bschulz1701/Project-Hedorah/Mechanical/Mrk 3 Body Assembly/VertMount.SLDASM

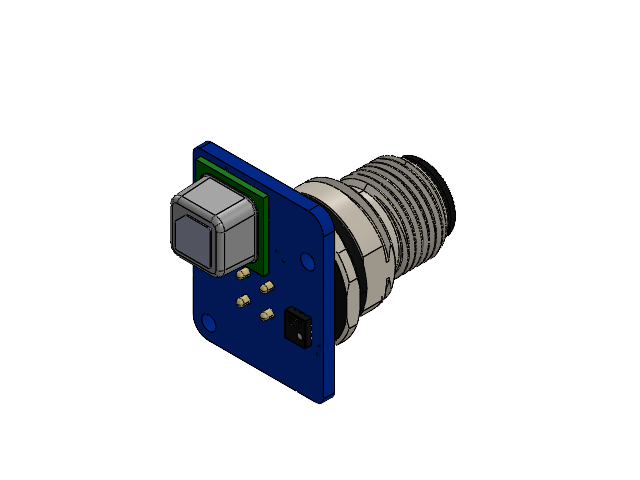
[picture p24: CAD file, 2024-09-26]
Mechanical/Mrk 3 Body Assembly/VertMount.SLDASM
Board.step
Sensirion_CO2_Sensors_SCD4x_STEP_file
STC31_STEP_file
c-t4140012041-000-b-3d
